steve-chamberlin/fpga-disk-controller/liron.asm

                  * = C700
C700   A2 20      LDX #$20
C702   A2 00      LDX #$00
C704   A2 03      LDX #$03
C706   C9 00      CMP #$00
C708   B0 0A      BCS $C714
C70A   38         SEC
C70B   B0 01      BCS $C70E
C70D   18         CLC
C70E   A2 07      LDX #$07
C710   7E 78 04   ROR $0478,X
C713   18         CLC
C714   A2 C7      LDX #$C7
C716   8E F8 07   STX $07F8
C719   A2 07      LDX #$07
C71B   AD FF CF   LDA $CFFF
C71E   4C E1 CB   JMP $CBE1
C721   A0 00      LDY #$00
C723   A5 4B      LDA $4B
C725   48         PHA
C726   D0 03      BNE $C72B
C728   4C B8 C7   JMP $C7B8
C72B   AD FC C0   LDA $C0FC
C72E   10 FB      BPL $C72B
C730   85 59      STA $59
C732   4A         LSR A
C733   4A         LSR A
C734   4A         LSR A
C735   29 0F      AND #$0F
C737   AA         TAX
C738   A5 59      LDA $59
C73A   29 07      AND #$07
C73C   85 59      STA $59
C73E   AD FC C0   LDA $C0FC
C741   10 FB      BPL $C73E
C743   5D 27 CA   EOR $CA27,X
C746   91 56      STA ($56),Y
C748   45 40      EOR $40
C74A   85 40      STA $40
C74C   C8         INY
C74D   D0 02      BNE $C751
C74F   E6 57      INC $57
C751   AD FC C0   LDA $C0FC
C754   10 FB      BPL $C751
C756   5D 37 CA   EOR $CA37,X
C759   91 56      STA ($56),Y
C75B   45 40      EOR $40
C75D   85 40      STA $40
C75F   C8         INY
C760   AD FC C0   LDA $C0FC
C763   10 FB      BPL $C760
C765   5D 47 CA   EOR $CA47,X
C768   91 56      STA ($56),Y
C76A   45 40      EOR $40
C76C   85 40      STA $40
C76E   C8         INY
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
CF53   FF         ???
CF54   FF         ???
CF55   FF         ???
CF56   FF         ???
CF57   FF         ???
CF58   FF         ???
CF59   FF         ???
CF5A   FF         ???
CF5B   FF         ???
CF5C   FF         ???
CF5D   FF         ???
CF5E   FF         ???
CF5F   FF         ???
CF60   FF         ???
CF61   FF         ???
CF62   FF         ???
CF63   FF         ???
CF64   FF         ???
CF65   FF         ???
CF66   FF         ???
CF67   FF         ???
CF68   FF         ???
CF69   FF         ???
CF6A   FF         ???
CF6B   FF         ???
CF6C   FF         ???
CF6D   FF         ???
CF6E   FF         ???
CF6F   FF         ???
CF70   FF         ???
CF71   FF         ???
CF72   FF         ???
CF73   FF         ???
CF74   FF         ???
CF75   FF         ???
CF76   FF         ???
CF77   FF         ???
CF78   FF         ???
CF79   FF         ???
CF7A   FF         ???
CF7B   FF         ???
CF7C   FF         ???
CF7D   FF         ???
CF7E   FF         ???
CF7F   FF         ???
CF80   FF         ???
CF81   FF         ???
CF82   FF         ???
CF83   FF         ???
CF84   FF         ???
CF85   FF         ???
CF86   FF         ???
CF87   FF         ???
CF88   FF         ???
CF89   FF         ???
CF8A   FF         ???
CF8B   FF         ???
CF8C   FF         ???
CF8D   FF         ???
CF8E   FF         ???
CF8F   FF         ???
CF90   FF         ???
CF91   FF         ???
CF92   FF         ???
CF93   FF         ???
CF94   FF         ???
CF95   FF         ???
CF96   FF         ???
CF97   FF         ???
CF98   FF         ???
CF99   FF         ???
CF9A   FF         ???
CF9B   FF         ???
CF9C   FF         ???
CF9D   FF         ???
CF9E   FF         ???
CF9F   FF         ???
CFA0   FF         ???
CFA1   FF         ???
CFA2   FF         ???
CFA3   FF         ???
CFA4   FF         ???
CFA5   FF         ???
CFA6   FF         ???
CFA7   FF         ???
CFA8   FF         ???
CFA9   FF         ???
CFAA   FF         ???
CFAB   FF         ???
CFAC   FF         ???
CFAD   FF         ???
CFAE   FF         ???
CFAF   FF         ???
CFB0   FF         ???
CFB1   FF         ???
CFB2   FF         ???
CFB3   FF         ???
CFB4   FF         ???
CFB5   FF         ???
CFB6   FF         ???
CFB7   FF         ???
CFB8   FF         ???
CFB9   FF         ???
CFBA   FF         ???
CFBB   FF         ???
CFBC   FF         ???
CFBD   FF         ???
CFBE   FF         ???
CFBF   FF         ???
CFC0   FF         ???
CFC1   FF         ???
CFC2   FF         ???
CFC3   FF         ???
CFC4   FF         ???
CFC5   FF         ???
CFC6   FF         ???
CFC7   FF         ???
CFC8   FF         ???
CFC9   FF         ???
CFCA   FF         ???
CFCB   FF         ???
CFCC   FF         ???
CFCD   FF         ???
CFCE   FF         ???
CFCF   FF         ???
CFD0   FF         ???
CFD1   FF         ???
CFD2   FF         ???
CFD3   FF         ???
CFD4   FF         ???
CFD5   FF         ???
CFD6   FF         ???
CFD7   FF         ???
CFD8   FF         ???
CFD9   FF         ???
CFDA   FF         ???
CFDB   A8         TAY
CFDC   C3         ???
CFDD   A9 A0      LDA #$A0
CFDF   B1 B9      LDA ($B9),Y
CFE1   B8         CLV
CFE2   B5 A0      LDA $A0,X
CFE4   C1 F0      CMP ($F0,X)
CFE6   F0 EC      BEQ $CFD4
CFE8   E5 A0      SBC $A0
CFEA   C3         ???
CFEB   EF         ???
CFEC   ED F0 F5   SBC $F5F0
CFEF   F4         ???
CFF0   E5 F2      SBC $F2
CFF2   AC A0 C9   LDY $C9A0
CFF5   EE E3 AE   INC $AEE3
CFF8   A0 CD      LDY #$CD
CFFA   D3         ???
CFFB   C1 00      CMP ($00,X)
CFFD   10 FF      BPL $CFFE
CFFF              .END
